simeonbabatunde/uv_risk_detection_and_prevention/software/integration_tests/radio_lights/display/display_unit.h

/*
 Problem - if we can access radio from a class, then we can't use the state machine as a class.
*/

#ifndef DISPLAY_UNIT_H_
#define DISPLAY_UNIT_H_

#include "Energia.h"

class Display_Unit
{
  public:
    Display_Unit();
    void receive_UV_data();
    void change_LEDs(); 
    void next();
    int getState();
    int byteToLight(const byte& toConvert);
  private:
    int state;
    byte curr_uv;
    byte avg_uv;

    //Led_Bar avg_bar();
    //Led_Bar curr_bar();
    
};


#endif
